wenbang24/volt/img/pcbv2.2_4.png

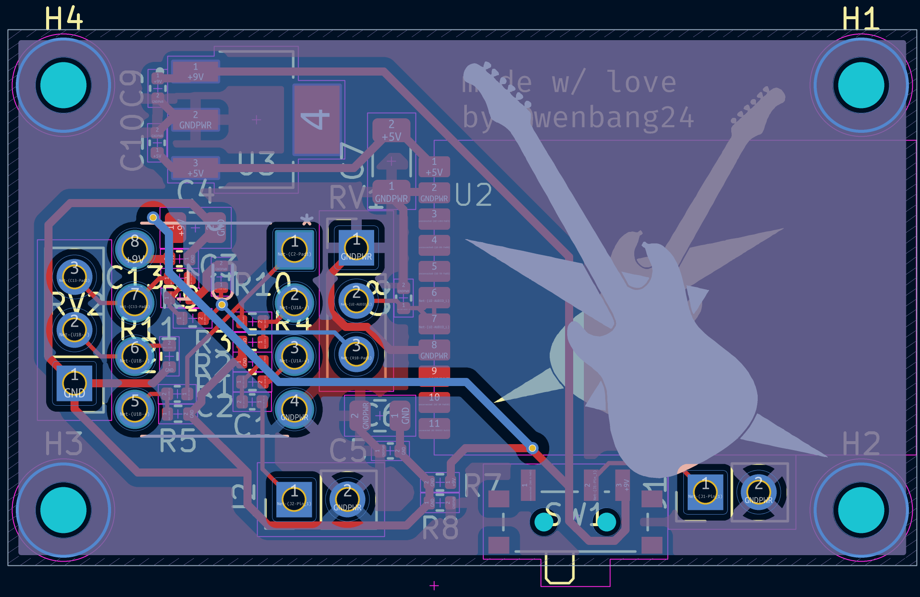
img/pcbv2.2_4.png
