wenbang24/volt/pcb/Volt.asc

C1: Cap; 1µ
C2: polcap; 47µ
C3: Cap; 100n
C4: polcap; 47µ
C5: Cap; 100n
C6: Cap; 4µ7
C7: Cap; 1µ
C8: cap; 10p
C9: cap; 10p
R1: Res; 100k
R2: Res; 100k
R3: Res; 1k
R4: Res; 100k
R5: Res; 4k7
R6: Res; 10k
R7: Res; 220k
R8: Res; 10k
R9: Res; 100k
R10: Res; 100k
R11: Res; 10k
R12: Res; 4k7
R13: Res; 100k
U3: TL072
U4: TL072
V1: signal; SINE(0 500m 2K)
V2: cell; 9
Named nets: 0, +9v, +4.5V, Va, Vout
.tran 1u 1m
